Stream-neverback/Klan-Mechanism-Robot/battery.SLDPRT

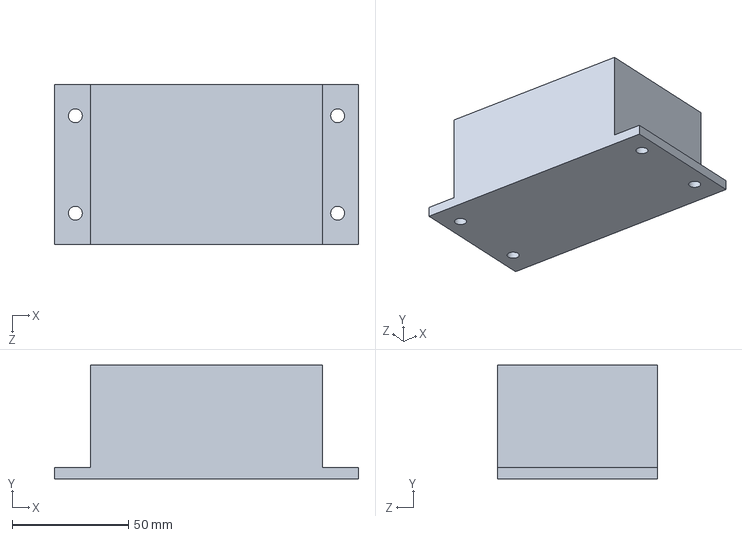
[picture p36: CAD file, 2022-06-04]
battery.SLDPRT
131.0 x 49.0 x 69.0 mm
