Stream-neverback/Klan-Mechanism-Robot/4x3mm整体构架板.DXF

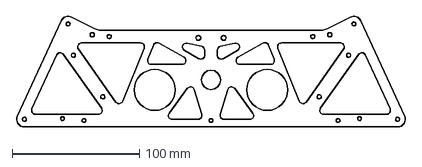
[picture p37: CAD file, 2022-06-04]
4x3mm整体构架板.DXF
306.1 x 87.2 mm
