Stream-neverback/Klan-Mechanism-Robot/动力连杆ManuGearSide.SLDPRT

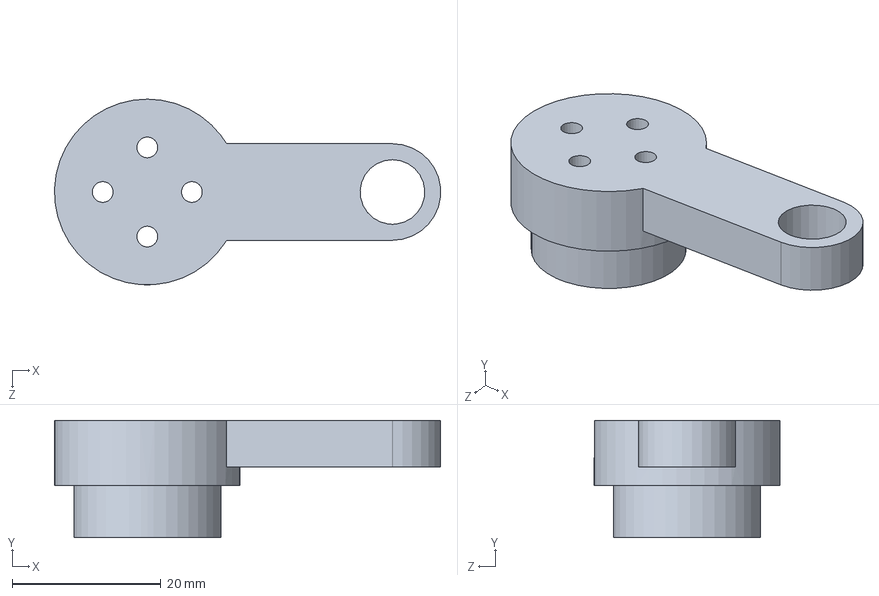
[picture p38: CAD file, 2022-06-04]
动力连杆ManuGearSide.SLDPRT
52.0 x 15.8 x 25.0 mm
