Stream-neverback/Klan-Mechanism-Robot/8x5mm腿.DXF

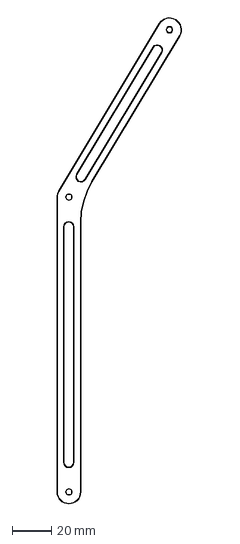
[picture p39: CAD file, 2022-06-04]
8x5mm腿.DXF
64.1 x 248.3 mm
