Stream-neverback/Klan-Mechanism-Robot/8x5mm上部连杆.DXF

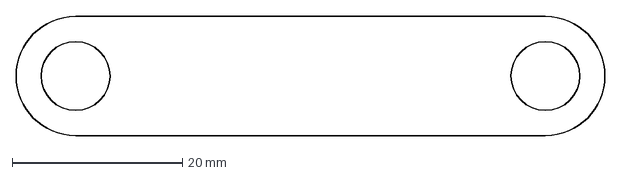
[picture p40: CAD file, 2022-06-04]
8x5mm上部连杆.DXF
69.3 x 14.0 mm
