Stream-neverback/Klan-Mechanism-Robot/M3螺母.SLDPRT

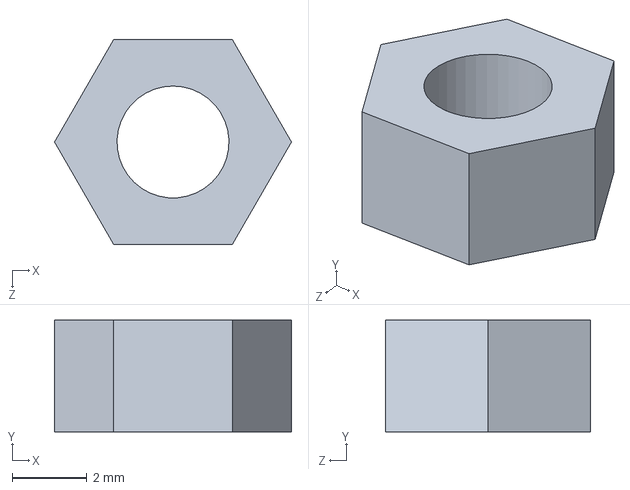
[picture p41: CAD file, 2022-06-04]
M3螺母.SLDPRT
6.35 x 3.00 x 5.50 mm
