Stream-neverback/Klan-Mechanism-Robot/螺丝M3_25.SLDPRT

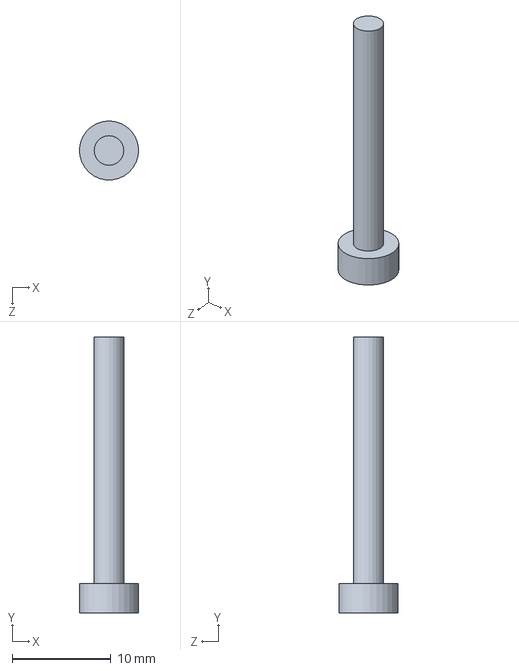
[picture p42: CAD file, 2022-06-04]
螺丝M3_25.SLDPRT
5.99 x 28.0 x 6.00 mm
