Stream-neverback/Klan-Mechanism-Robot/边缘垫套筒.SLDPRT

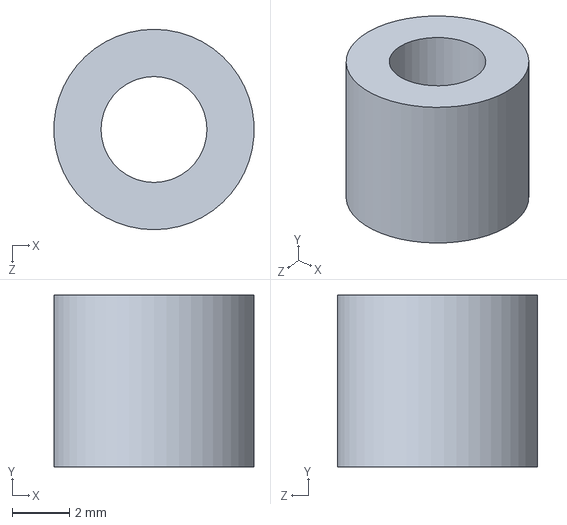
[picture p43: CAD file, 2022-06-04]
边缘垫套筒.SLDPRT
6.99 x 6.00 x 7.00 mm
