Stream-neverback/Klan-Mechanism-Robot/8x5mm中间三孔连杆.DXF

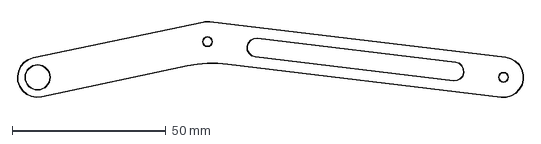
[picture p44: CAD file, 2022-06-04]
8x5mm中间三孔连杆.DXF
165.2 x 25.0 mm
