Stream-neverback/Klan-Mechanism-Robot/X型加强件Botton.SLDPRT

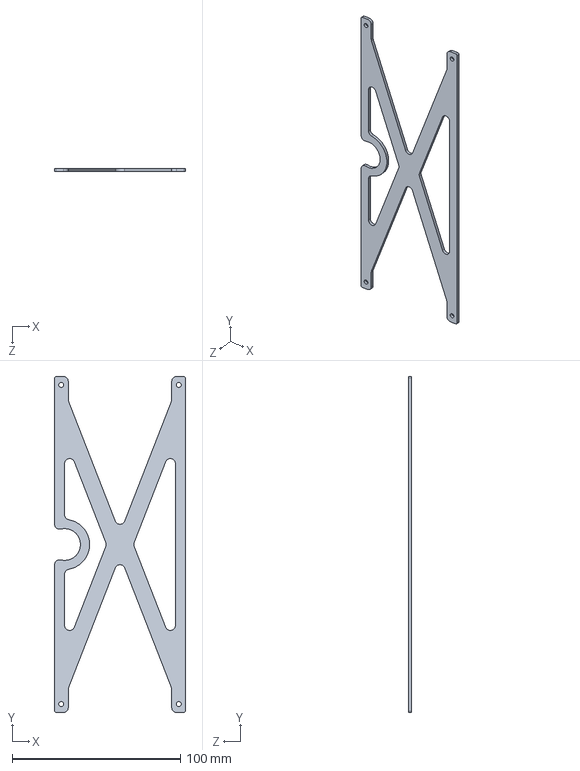
[picture p45: CAD file, 2022-06-04]
X型加强件Botton.SLDPRT
78.0 x 200.0 x 2.00 mm
