Stream-neverback/Klan-Mechanism-Robot/底板.SLDPRT

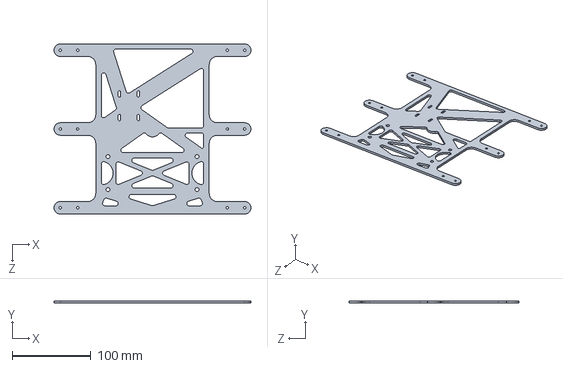
[picture p46: CAD file, 2022-06-04]
底板.SLDPRT
250.0 x 3.00 x 216.0 mm
