Stream-neverback/Klan-Mechanism-Robot/动力连杆ManuGear.SLDPRT

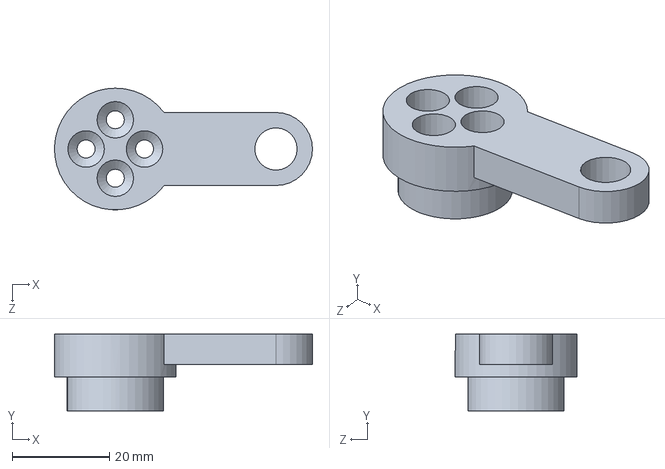
[picture p47: CAD file, 2022-06-04]
动力连杆ManuGear.SLDPRT
53.0 x 15.8 x 25.0 mm
