Stream-neverback/Klan-Mechanism-Robot/六角轴套.SLDPRT

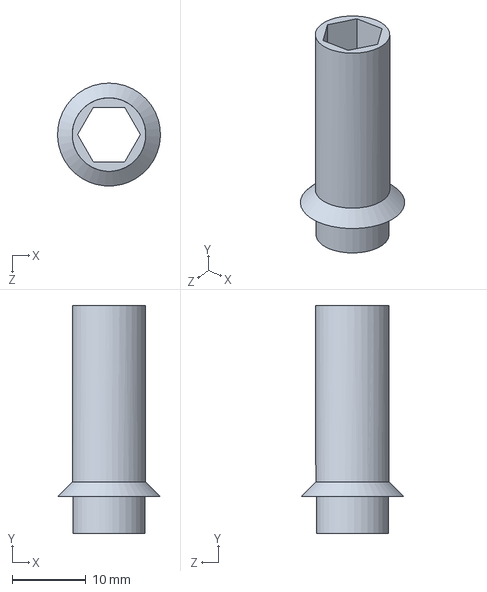
[picture p48: CAD file, 2022-06-04]
六角轴套.SLDPRT
14.0 x 31.0 x 14.0 mm
