Stream-neverback/Klan-Mechanism-Robot/腿.SLDPRT

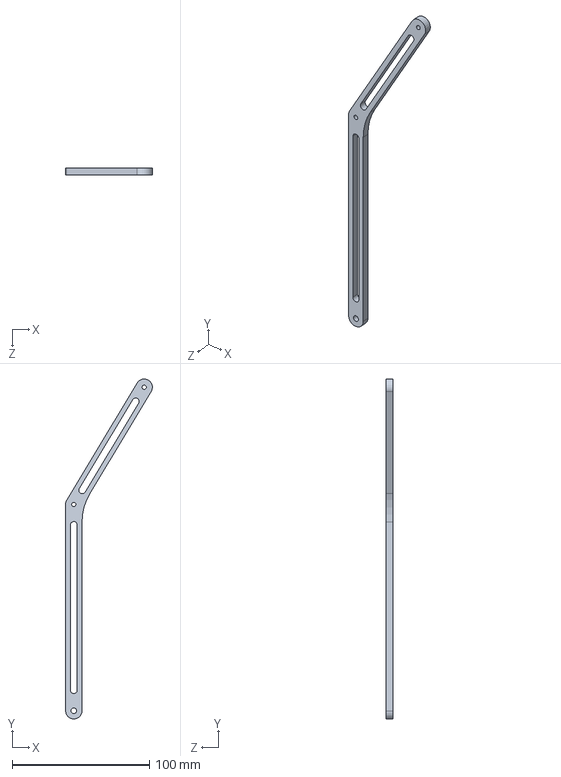
[picture p49: CAD file, 2022-06-04]
腿.SLDPRT
63.2 x 247.5 x 5.00 mm
