Stream-neverback/Klan-Mechanism-Robot/电机架.SLDPRT

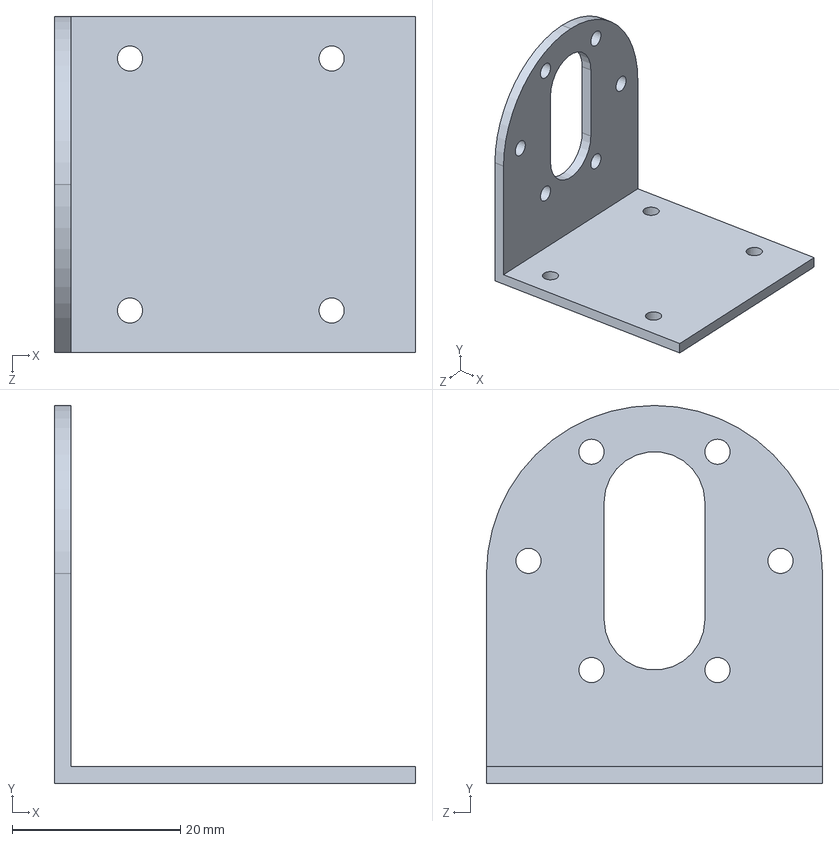
[picture p50: CAD file, 2022-06-04]
电机架.SLDPRT
43.0 x 45.0 x 40.0 mm
