Stream-neverback/Klan-Mechanism-Robot/8x5mm底无动力连杆.DXF

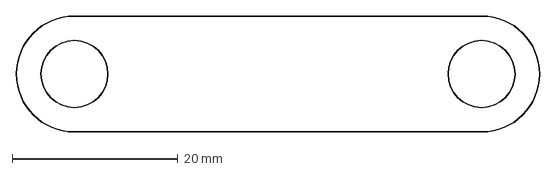
[picture p51: CAD file, 2022-06-04]
8x5mm底无动力连杆.DXF
63.2 x 14.0 mm
