Stream-neverback/Klan-Mechanism-Robot/垫片3_7_0.5.SLDPRT

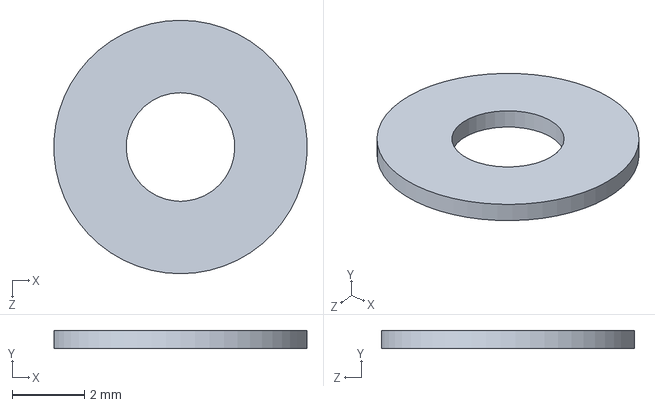
[picture p52: CAD file, 2022-06-04]
垫片3_7_0.5.SLDPRT
6.99 x 0.5 x 7.00 mm
