Stream-neverback/Klan-Mechanism-Robot/1x3mm底板.DXF

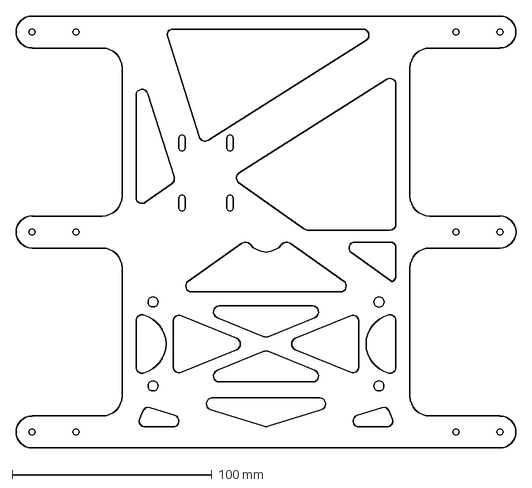
[picture p53: CAD file, 2022-06-04]
1x3mm底板.DXF
250.0 x 216.0 mm
