Stream-neverback/Klan-Mechanism-Robot/Shaft直齿M1.5X28.SLDPRT

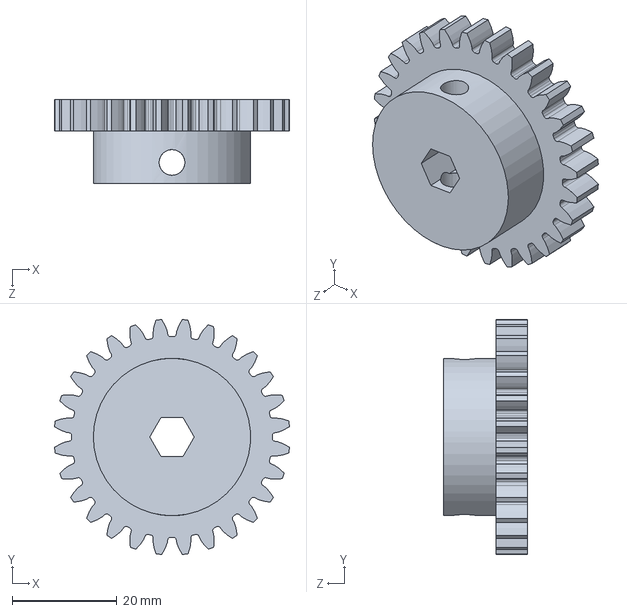
[picture p54: CAD file, 2022-06-04]
Shaft直齿M1.5X28.SLDPRT
44.8 x 44.8 x 16.0 mm
