Stream-neverback/Klan-Mechanism-Robot/1x2mmX型加强件.DXF

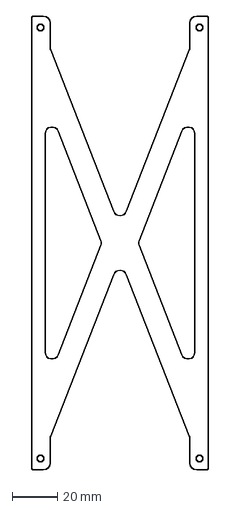
[picture p55: CAD file, 2022-06-04]
1x2mmX型加强件.DXF
78.0 x 200.0 mm
