Stream-neverback/Klan-Mechanism-Robot/动力连杆.SLDPRT

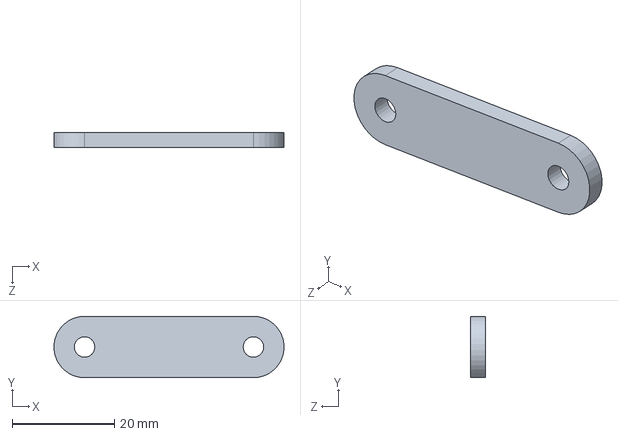
[picture p56: CAD file, 2022-06-04]
动力连杆.SLDPRT
44.9 x 12.0 x 3.00 mm
