Stream-neverback/Klan-Mechanism-Robot/六角轴10MM300L.SLDPRT

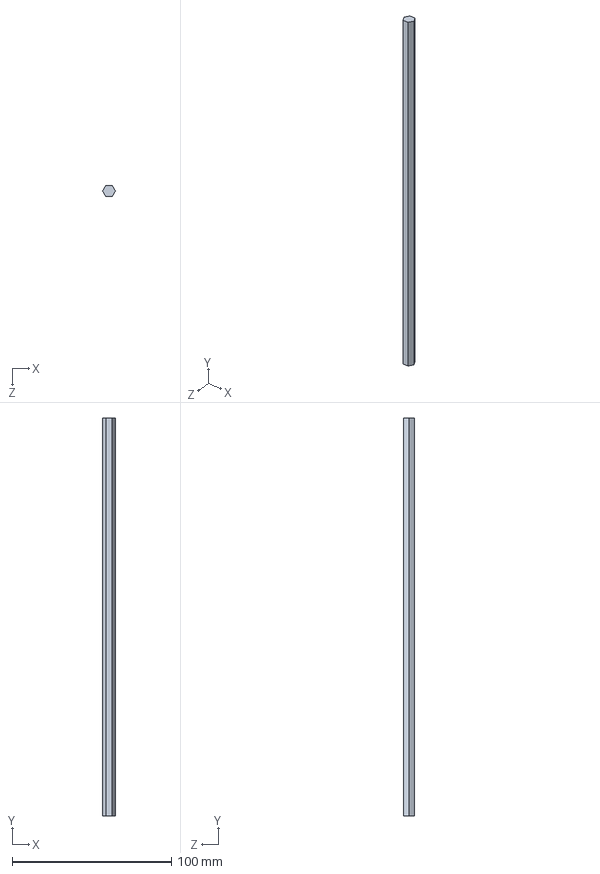
[picture p57: CAD file, 2022-06-04]
六角轴10MM300L.SLDPRT
8.08 x 250.0 x 7.00 mm
