Stream-neverback/Klan-Mechanism-Robot/轴套3_d7_H10.SLDPRT

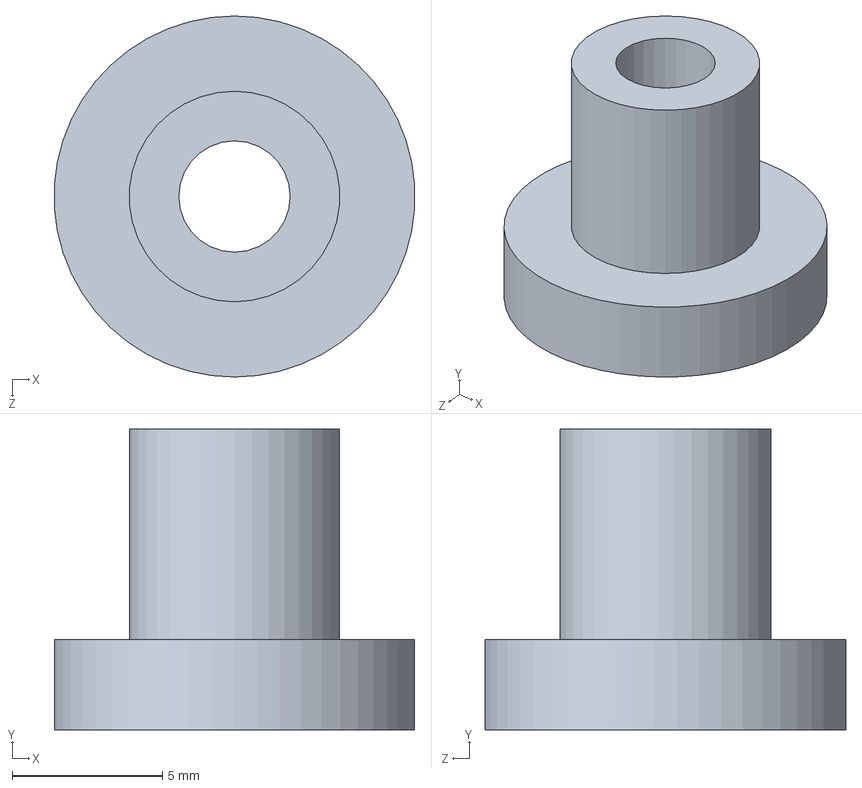
[picture p58: CAD file, 2022-06-04]
轴套3_d7_H10.SLDPRT
12.0 x 10.0 x 12.0 mm
