Stream-neverback/Klan-Mechanism-Robot/边侧齿轮L2直齿M1.5X30.SLDPRT

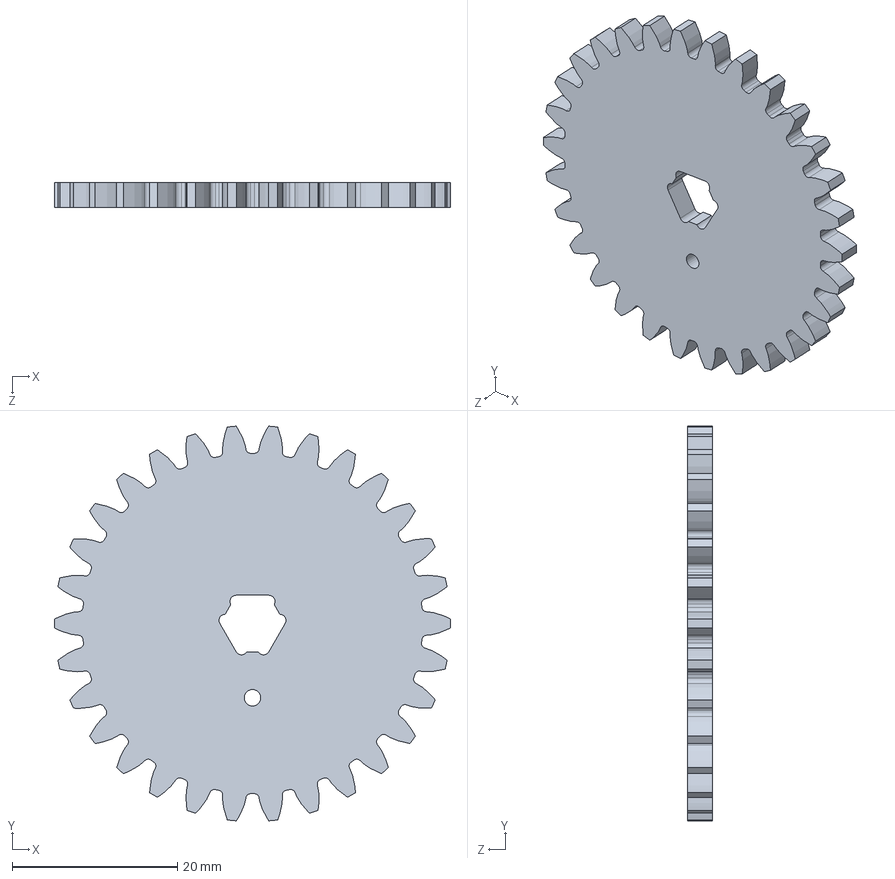
[picture p59: CAD file, 2022-06-04]
边侧齿轮L2直齿M1.5X30.SLDPRT
48.0 x 47.8 x 3.00 mm
