Stream-neverback/Klan-Mechanism-Robot/2x4mm边侧齿轮L2直齿M1.5X30.DXF

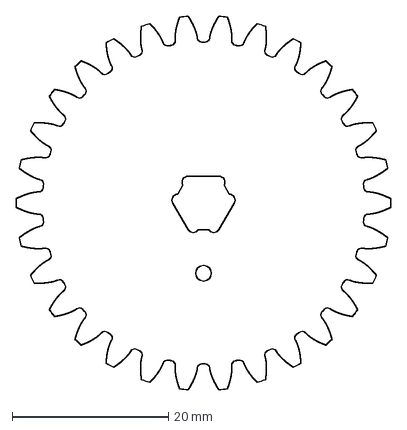
[picture p60: CAD file, 2022-06-04]
2x4mm边侧齿轮L2直齿M1.5X30.DXF
48.0 x 47.8 mm
