Stream-neverback/Klan-Mechanism-Robot/中间三孔连杆.SLDPRT

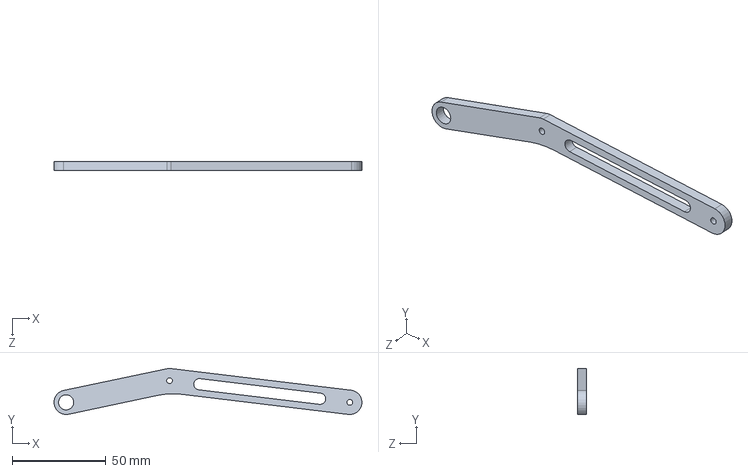
[picture p61: CAD file, 2022-06-04]
中间三孔连杆.SLDPRT
164.4 x 24.6 x 5.00 mm
