Stream-neverback/Klan-Mechanism-Robot/底无动力连杆.SLDPRT

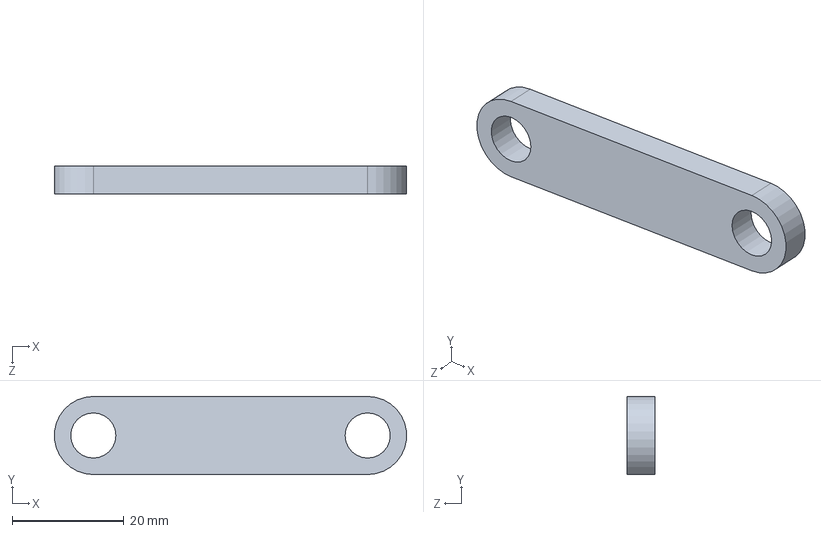
[picture p62: CAD file, 2022-06-04]
底无动力连杆.SLDPRT
63.1 x 14.0 x 5.00 mm
