Stream-neverback/Klan-Mechanism-Robot/腿部齿轮L3直齿M1.5X301.SLDPRT

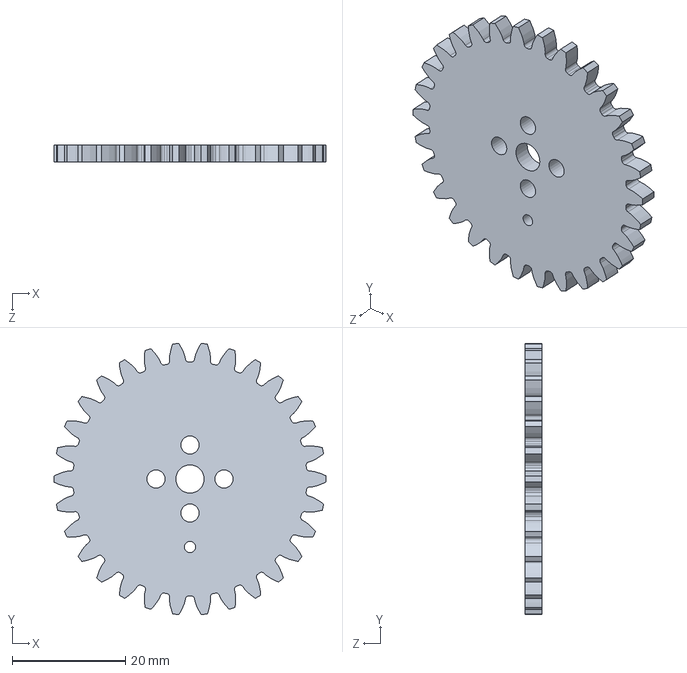
[picture p63: CAD file, 2022-06-04]
腿部齿轮L3直齿M1.5X301.SLDPRT
48.0 x 47.8 x 3.00 mm
