Stream-neverback/Klan-Mechanism-Robot/法兰轴承3_8_9.5_H4_F1.SLDPRT

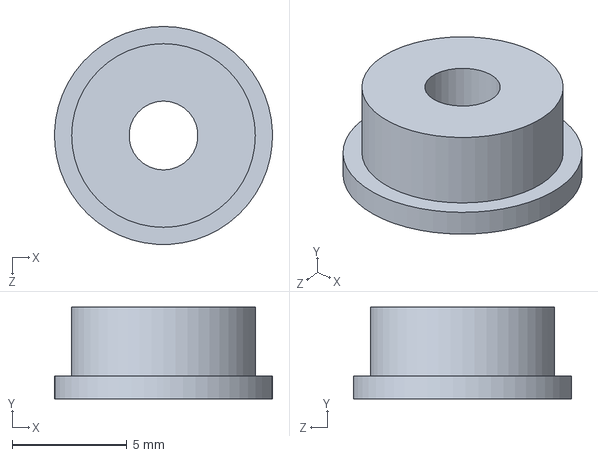
[picture p64: CAD file, 2022-06-04]
法兰轴承3_8_9.5_H4_F1.SLDPRT
9.50 x 4.00 x 9.50 mm
