Stream-neverback/Klan-Mechanism-Robot/法兰轴承10_15_4_0.8.SLDPRT

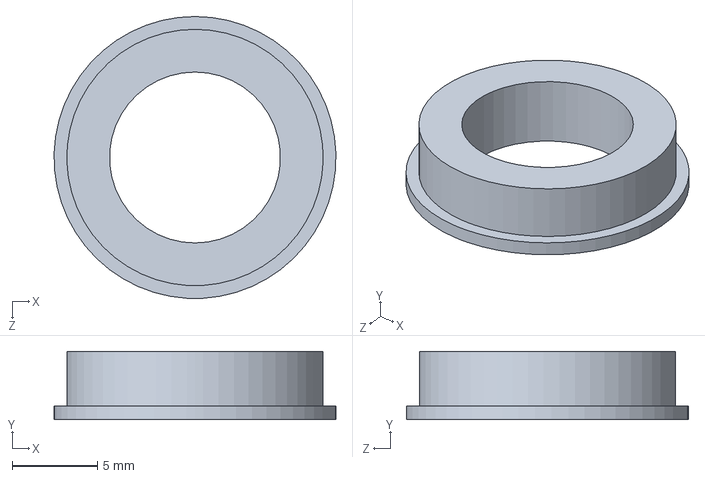
[picture p65: CAD file, 2022-06-04]
法兰轴承10_15_4_0.8.SLDPRT
16.5 x 4.00 x 16.5 mm
