Stream-neverback/Klan-Mechanism-Robot/六面螺母M3_10.SLDPRT

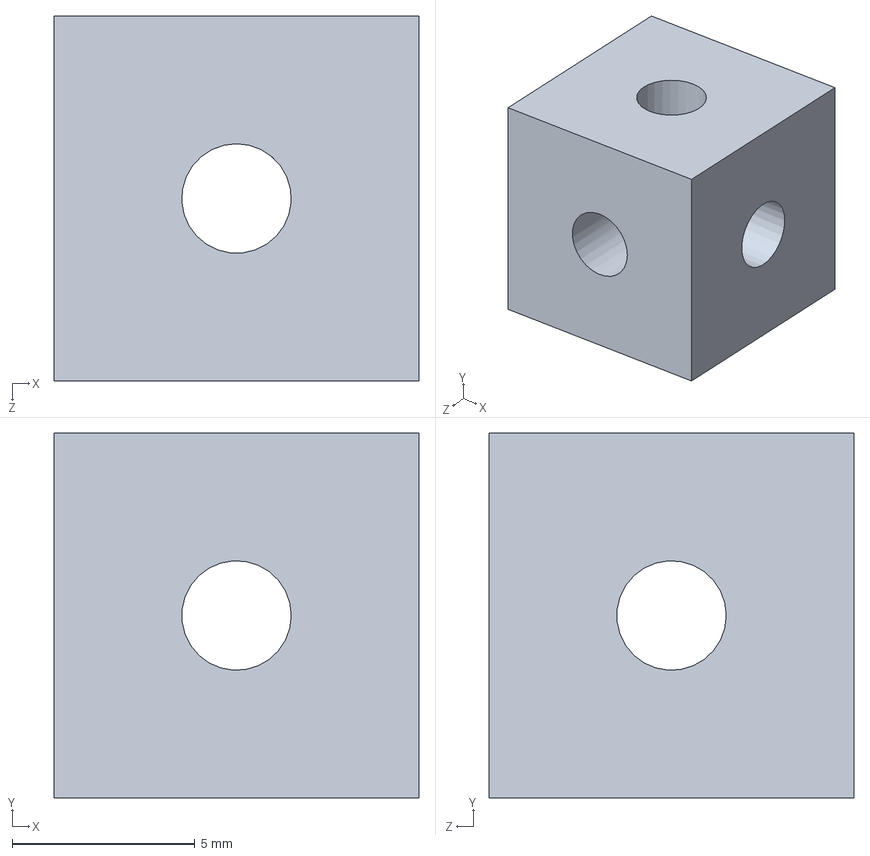
[picture p66: CAD file, 2022-06-04]
六面螺母M3_10.SLDPRT
10.0 x 10.0 x 10.0 mm
