Stream-neverback/Klan-Mechanism-Robot/4x3mm腿部齿轮L3直齿M1.5X30.DXF

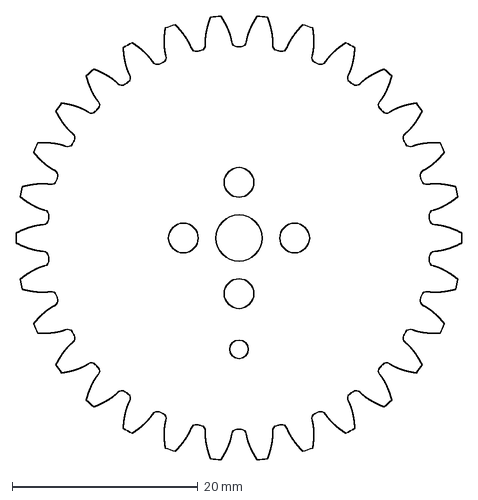
[picture p67: CAD file, 2022-06-04]
4x3mm腿部齿轮L3直齿M1.5X30.DXF
48.0 x 47.8 mm
