Stream-neverback/Klan-Mechanism-Robot/上部连杆.SLDPRT

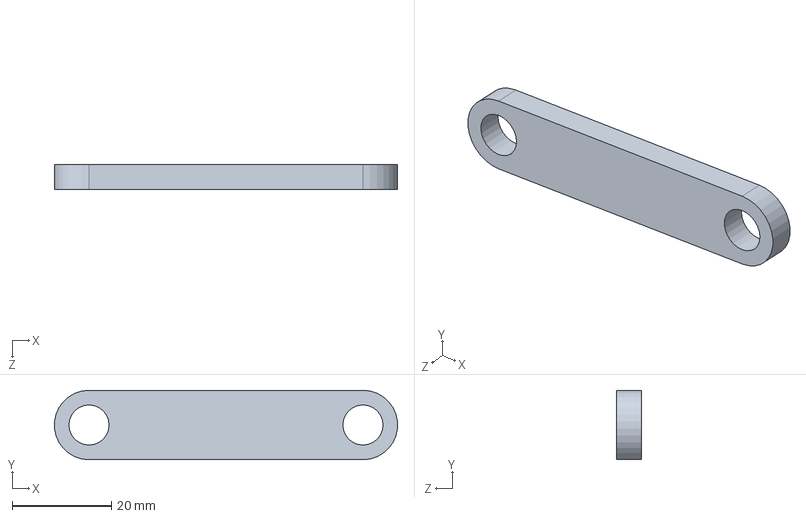
[picture p68: CAD file, 2022-06-04]
上部连杆.SLDPRT
69.2 x 14.0 x 5.00 mm
