Stream-neverback/Klan-Mechanism-Robot/Motore直齿M1.5X12.SLDPRT

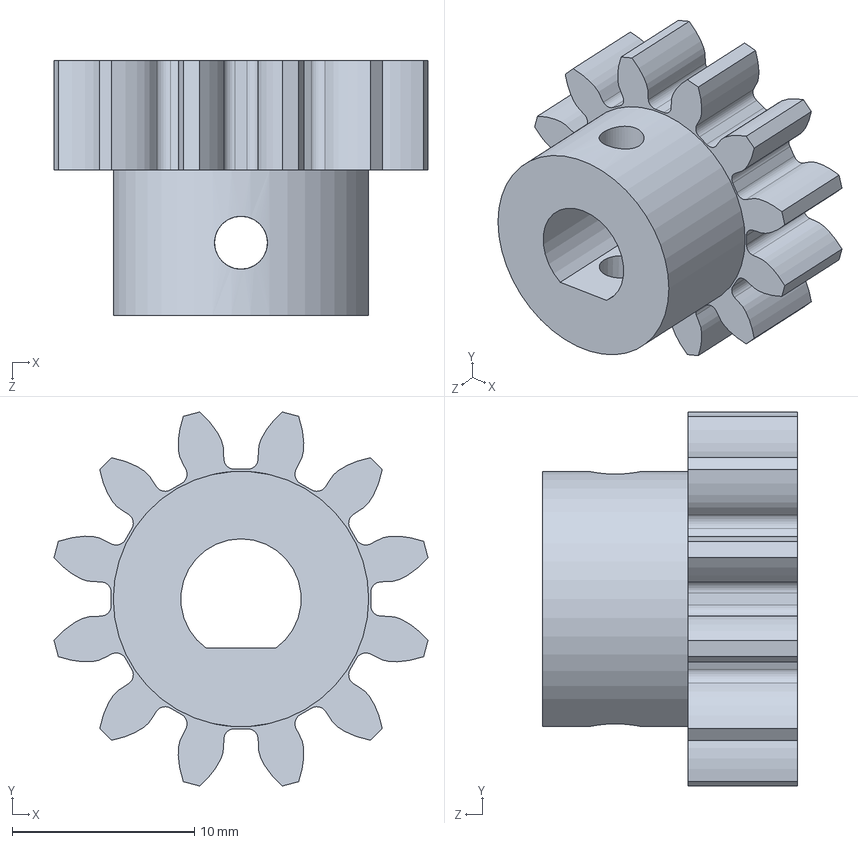
[picture p69: CAD file, 2022-06-04]
Motore直齿M1.5X12.SLDPRT
20.5 x 20.5 x 14.0 mm
