Stream-neverback/Klan-Mechanism-Robot/AM六角轴10MM300L.SLDPRT

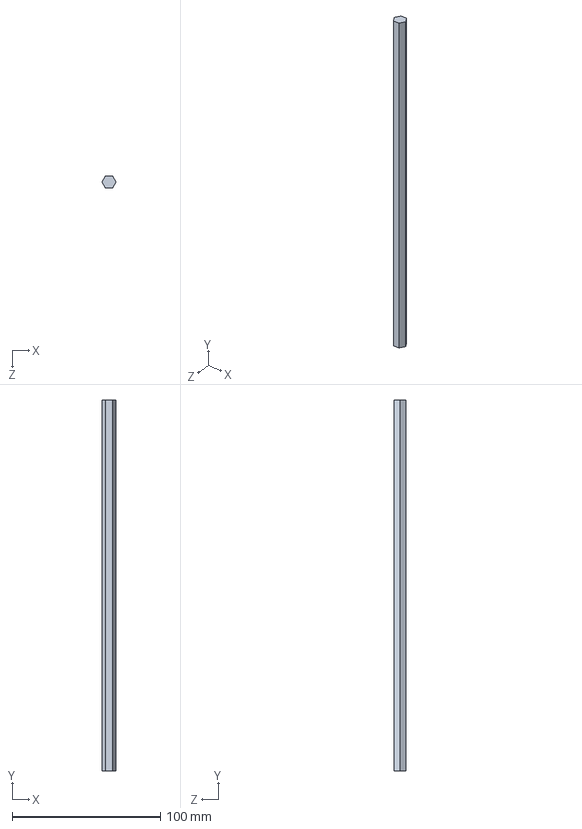
[picture p70: CAD file, 2022-06-04]
AM六角轴10MM300L.SLDPRT
9.60 x 250.0 x 8.31 mm
