Stream-neverback/Klan-Mechanism-Robot/动力连杆Manu.SLDPRT

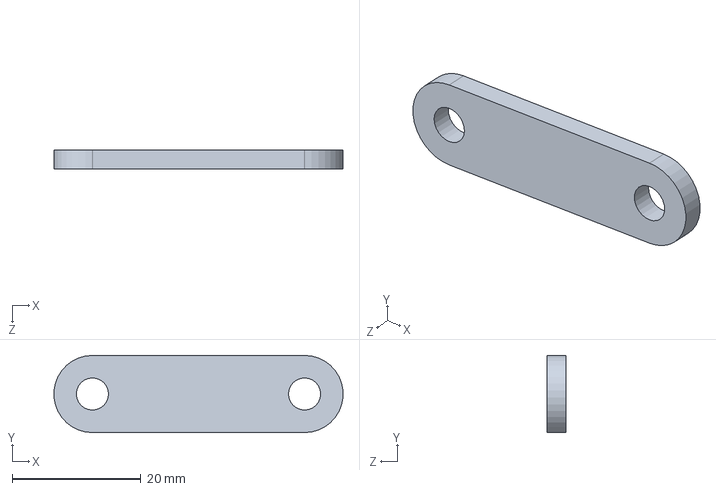
[picture p71: CAD file, 2022-06-04]
动力连杆Manu.SLDPRT
44.9 x 12.0 x 3.00 mm
