Stream-neverback/Klan-Mechanism-Robot/足端.sldprt

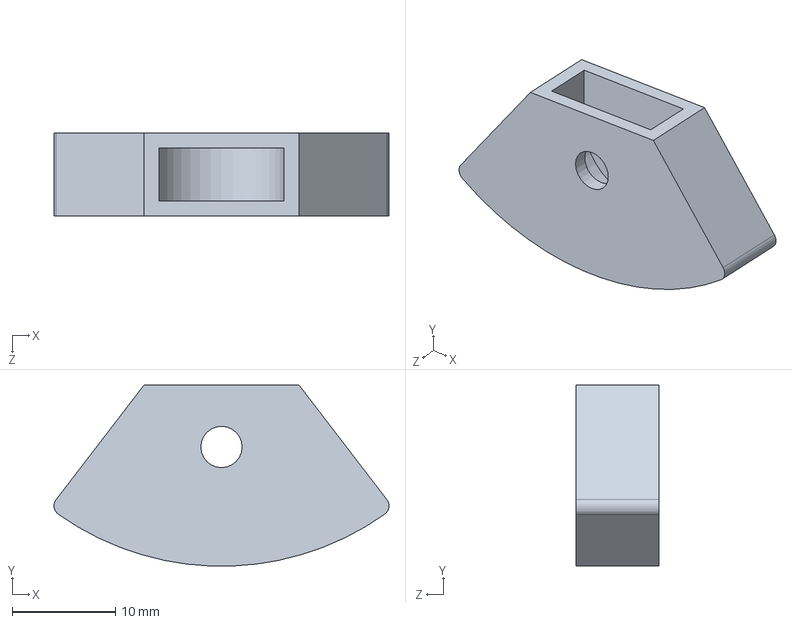
[picture p72: CAD file, 2022-06-04]
足端.sldprt
32.4 x 17.5 x 8.00 mm
