Stream-neverback/Klan-Mechanism-Robot/整体构架Manu.SLDPRT

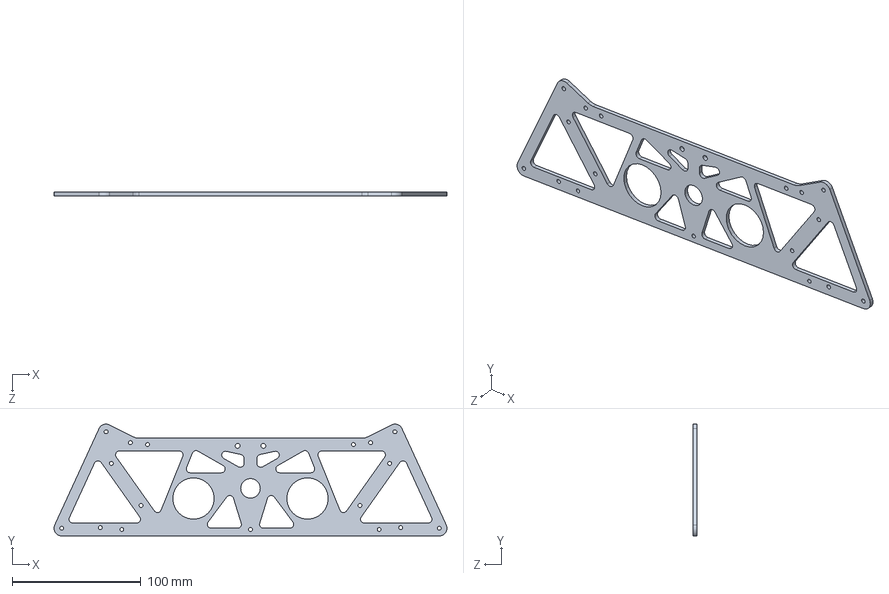
[picture p73: CAD file, 2022-06-04]
整体构架Manu.SLDPRT
305.4 x 87.0 x 3.00 mm
